Derpythederp/3.007-DTI-Cube/Kicad_bin/DTI_Cube_Proto.kicad_pcb

## KiCad design kicad/power-reset-module/power-reset-module.kicad_sch

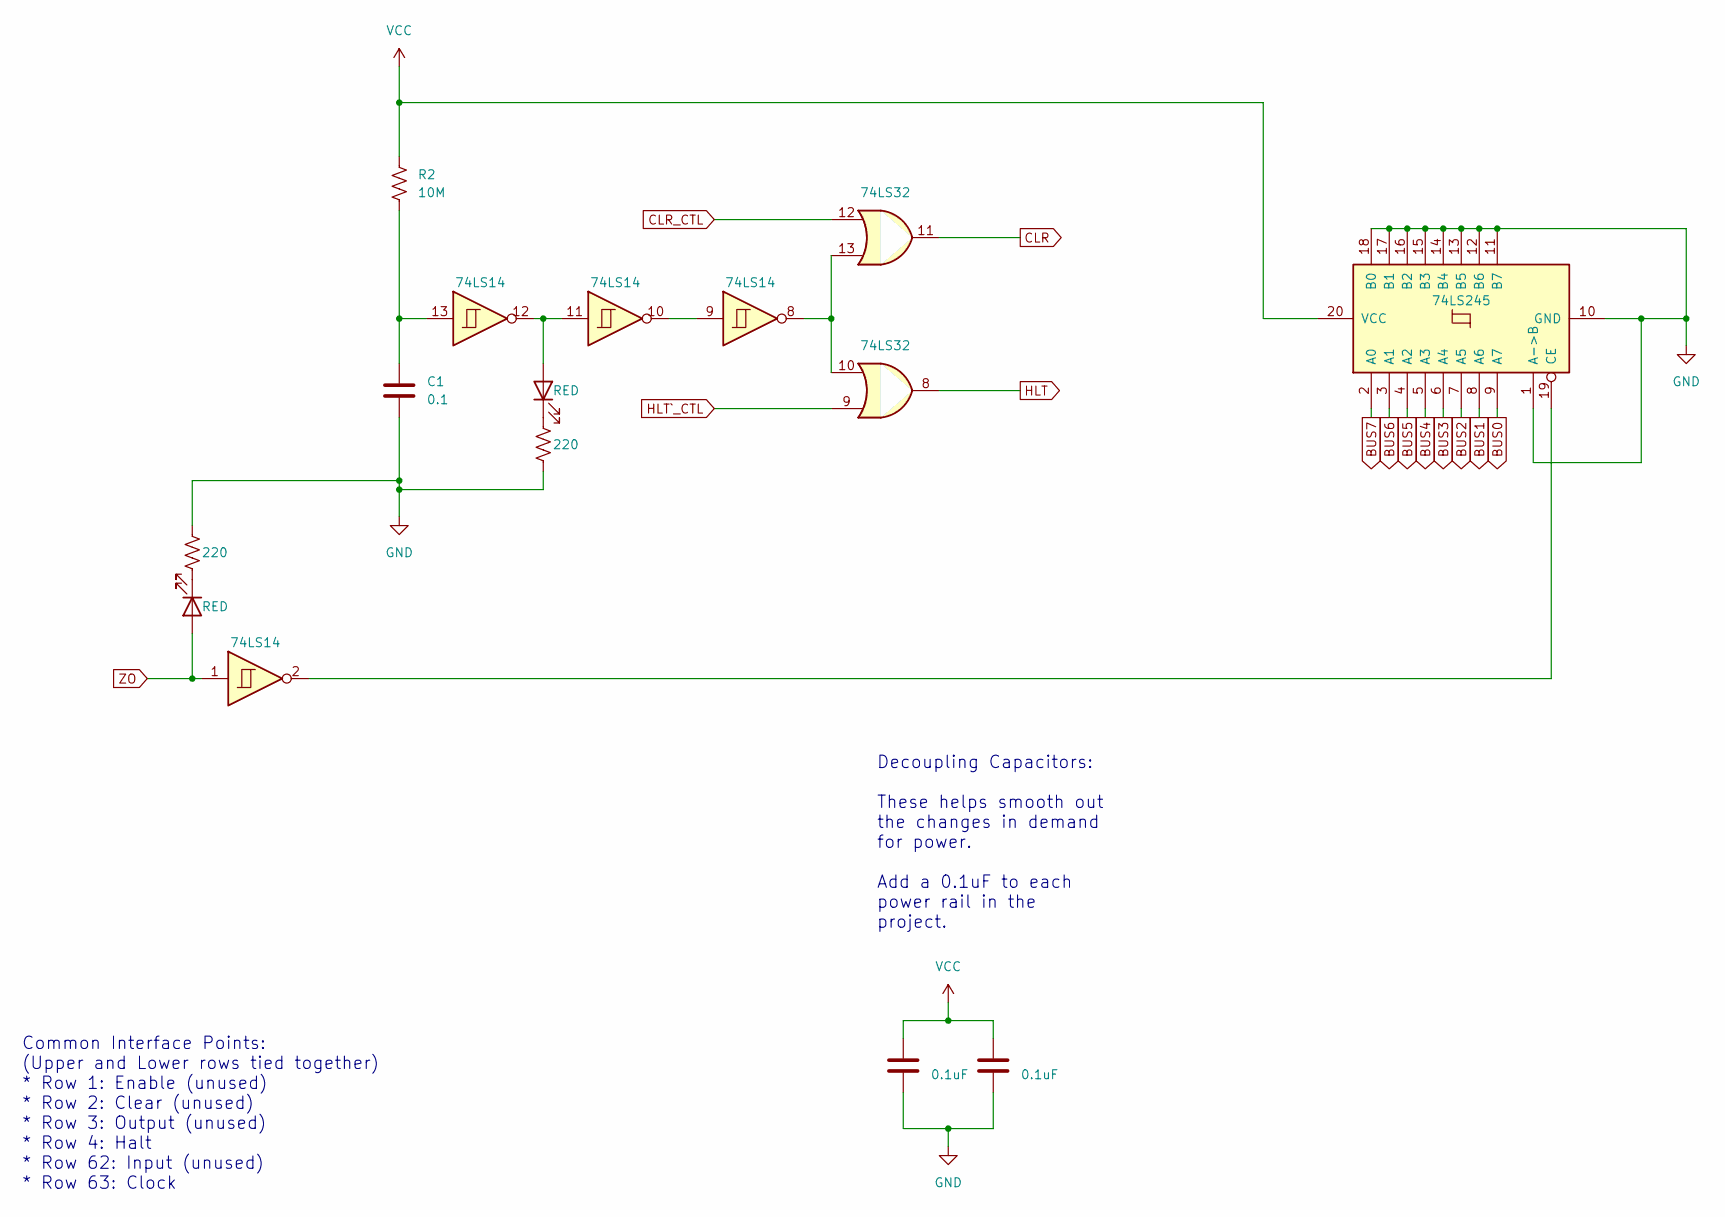
[picture p9: schematic power-reset-module.kicad_sch]

Parts:
C1: 0.1
D1, D2: RED
R1, R3: 220
R2: 10M
U1: 74LS14
U2: 74LS32
U3: 74LS245

Connections:
BUS0: U3.9 (A7)
BUS1: U3.8 (A6)
BUS2: U3.7 (A5)
BUS3: U3.6 (A4)
BUS4: U3.5 (A3)
BUS5: U3.4 (A2)
BUS6: U3.3 (A1)
BUS7: U3.2 (A0)
CLR: U2.11
CLR_CTL: U2.12
GND: C1.2, R1.1, R3.2, U3.1 (A->B), U3.10 (GND), U3.11 (B7), U3.12 (B6), U3.13 (B5), U3.14 (B4), U3.15 (B3), U3.16 (B2), U3.17 (B1), U3.18 (B0)
HLT: U2.8
HLT`_CTL: U2.9
unnamed: C1.1, R2.2, U1.13
unnamed: D1.1 (K), R1.2
unnamed: D2.1 (K), R3.1
unnamed: D2.2 (A), U1.11, U1.12
unnamed: U1.2, U3.19 (CE)
unnamed: U1.8, U2.10, U2.13
unnamed: U1.9, U1.10
VCC: R2.1, U3.20 (VCC)
ZO: D1.2 (A), U1.1

Notes on the sheet:
Decoupling Capacitors: These helps smooth out the changes in demand for power. Add a 0.1uF to each power rail in the project.
Common Interface Points: (Upper and Lower rows tied together) * Row 1: Enable (unused) * Row 2: Clear (unused) * Row 3: Output (unused) * Row 4: Halt * Row 62: Input (unused) * Row 63: Clock
